ondrasouk/Digital-electronics-2-project/src/doxy_main.h

/**
 * @mainpage    Dokumentace
 * 
 * @section Oveeall data
 * @author      Pavel Vanek
 * @author      Ondrej Soukenik
<<<<<<< HEAD:src/doxy_main.h
 * @author      Zuzana Varmuzova
 * @author      Michaela Rysava
=======
 * @author      Zdenka Varmuzova
 * @author      Michaela Ryšava
>>>>>>> df13011e5b6e7a4a76afdd674e0574bcf85c4329:doxy_main.txt
 * 
 * @date    16.12.2021
 * 
 * 
 * @section Project
 * @brief   Automatic Watering system is implemented on Arduino Uno Board. 
 * @details Main function is controling humidity of soil and controling of pump system when humidity level drops below 60%
 * @details Application includes sensor for measuring water level, RTC for time controla nd LCD display with move buttons
 */
/**
 * @defgroup hum    Humidity sensor
 * @brief    Functions for controling himidity sensor
 * @defgroup water  Water level sensor
 * @brief    Functions for controling water level sensor
 * @defgroup rtc    RTC
 * @brief    Functions for communication with RTC
 * @defgroup lcd    LCD display
 * @brief    Functions for communication with LCD display
 * @defgroup pump   Pump control
 * @brief    Functions for controling Pump
 */
 /**
